owenCocjin/HardVault/Arduino/arrows.h

//Author:  Owen Cocjin
//Version: 1.0
//Date:    02/02/2021
//Description:  Stores arrow icon data
//Notes:
//Struct for big arrow graphics
struct Big_Arrow{
	uint8_t top[16];
	uint8_t bottom[16];
};//Big_arrow

Big_Arrow Arrow_Left={{0x80, 0xc0, 0xe0, 0xf0, 0xf8, 0xfc, 0xfe, 0xff, 0xc0, 0xc0, 0xc0, 0xc0, 0xc0, 0xc0, 0xc0, 0xc0},
{0x01, 0x03, 0x07, 0x0f, 0x1f, 0x3f, 0x7f, 0xff, 0x03, 0x03, 0x03, 0x03, 0x03, 0x03, 0x03, 0x03}};
Big_Arrow Arrow_Up={{0x80, 0xc0, 0xe0, 0xf0, 0xf8, 0xfc, 0xfe, 0xff, 0xff, 0xfe, 0xfc, 0xf8, 0xf0, 0xe0, 0xc0, 0x80},
{0x00, 0x00, 0x00, 0x00, 0x00, 0x00, 0xff, 0xff, 0xff, 0xff, 0x00, 0x00, 0x00, 0x00, 0x00, 0x00}};
Big_Arrow Arrow_Right={{0xc0, 0xc0, 0xc0, 0xc0, 0xc0, 0xc0, 0xc0, 0xc0, 0xff, 0xfe, 0xfc, 0xf8, 0xf0, 0xe0, 0xc0, 0x80},
{0x03, 0x03, 0x03, 0x03, 0x03, 0x03, 0x03, 0x03, 0xff, 0x7f, 0x3f, 0x1f, 0x0f, 0x07, 0x03, 0x01}};
Big_Arrow Arrow_Down={{0x00, 0x00, 0x00, 0x00, 0x00, 0x00, 0xff, 0xff, 0xff, 0xff, 0x00, 0x00, 0x00, 0x00, 0x00, 0x00},
{0x01, 0x03, 0x07, 0x0f, 0x1f, 0x3f, 0x7f, 0xff, 0xff, 0x7f, 0x3f, 0x1f, 0x0f, 0x07, 0x03, 0x01}};

Big_Arrow Arrow_Up_inv={{0xff, 0xff, 0x3f, 0x1f, 0x0f, 0x07, 0x03, 0x01, 0x01, 0x03, 0x07, 0x0f, 0x1f, 0x3f, 0xff, 0xff},
{0xff, 0xff, 0xff, 0xff, 0xff, 0xff, 0x80, 0x80, 0x80, 0x80, 0xff, 0xff, 0xff, 0xff, 0xff, 0xff}};
Big_Arrow Arrow_Down_inv={{0xff, 0xff, 0xff, 0xff, 0xff, 0xff, 0x01, 0x01, 0x01, 0x01, 0xff, 0xff, 0xff, 0xff, 0xff, 0xff},
{0xff, 0xff, 0xfc, 0xf8, 0xf0, 0xe0, 0xc0, 0x80, 0x80, 0xc0, 0xe0, 0xf0, 0xf8, 0xfc, 0xff, 0xff}};
Big_Arrow Arrow_Left_inv={{0xff, 0x7f, 0x3f, 0x1f, 0x0f, 0x07, 0x03, 0x03, 0x3f, 0x3f, 0x3f, 0x3f, 0x3f, 0x3f, 0x3f, 0xff},
{0xff, 0xfe, 0xfc, 0xf8, 0xf0, 0xe0, 0xc0, 0xc0, 0xfc, 0xfc, 0xfc, 0xfc, 0xfc, 0xfc, 0xfc, 0xff}};
Big_Arrow Arrow_Right_inv={{0xff, 0x3f, 0x3f, 0x3f, 0x3f, 0x3f, 0x3f, 0x3f, 0x03, 0x03, 0x07, 0x0f, 0x1f, 0x3f, 0x7f, 0xff},
{0xff, 0xfc, 0xfc, 0xfc, 0xfc, 0xfc, 0xfc, 0xfc, 0xc0, 0xc0, 0xe0, 0xf0, 0xf8, 0xfc, 0xfe, 0xff}};
//Array of all arrow positions
Big_Arrow arrow_pos[]={Arrow_Left,
	Arrow_Up,
	Arrow_Right,
	Arrow_Down,
	Arrow_Left_inv,
	Arrow_Up_inv,
	Arrow_Right_inv,
	Arrow_Down_inv};
